giomf/Promatrix-4000-IO/firmware/build.rs

//! This build script copies the `memory.x` file from the crate root into
//! a directory where the linker can always find it at build time, and sets
//! up the linker arguments required by embassy-rp / cortex-m-rt.

use std::env;
use std::fs::File;
use std::io::Write;
use std::path::PathBuf;

fn main() {
    // Put `memory.x` in our output directory and ensure it's on the linker
    // search path.
    let out = &PathBuf::from(env::var_os("OUT_DIR").unwrap());
    File::create(out.join("memory.x"))
        .unwrap()
        .write_all(include_bytes!("memory.x"))
        .unwrap();
    println!("cargo:rustc-link-search={}", out.display());

    // Only re-run the build script when memory.x is changed.
    println!("cargo:rerun-if-changed=memory.x");

    println!("cargo:rustc-link-arg-bins=--nmagic");
    println!("cargo:rustc-link-arg-bins=-Tlink.x");
    println!("cargo:rustc-link-arg-bins=-Tlink-rp.x");
}
