giomf/Promatrix-4000-IO/firmware/src/channels.rs

//! Channels used to shuttle [`protocol::Command`]s and [`protocol::Event`]s
//! between tasks.

use embassy_sync::blocking_mutex::raw::CriticalSectionRawMutex;
use embassy_sync::channel::Channel;
use protocol::{Command, Event};

/// Commands parsed from the USB host, waiting to be applied to the outputs.
pub static COMMANDS: Channel<CriticalSectionRawMutex, Command, 8> = Channel::new();
/// Events waiting to be sent to the USB host.
pub static EVENTS: Channel<CriticalSectionRawMutex, Event, 16> = Channel::new();
